githubgilhad/MegaHomeFORTH/docs/MHF-002/ATmega-Stacks.png

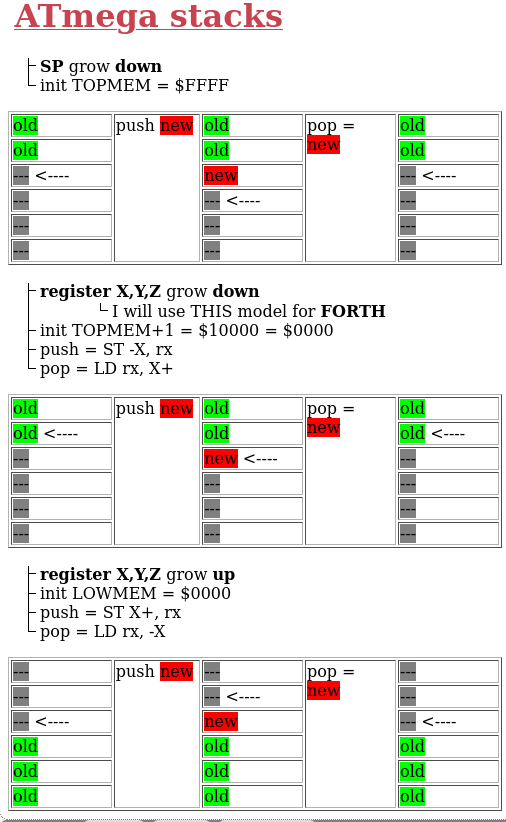
docs/MHF-002/ATmega-Stacks.png
