githubgilhad/MegaHomeFORTH/docs/MHF-002/config_gates.png

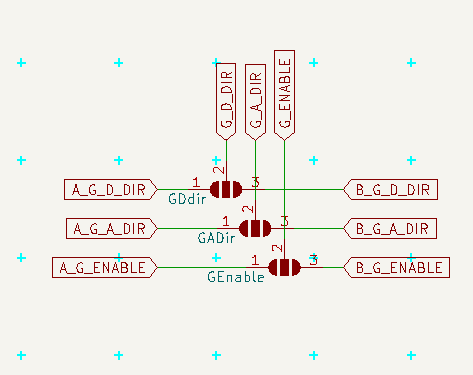
docs/MHF-002/config_gates.png
