githubgilhad/MegaHomeFORTH/docs/MHF-002/config_GLUE_top.png

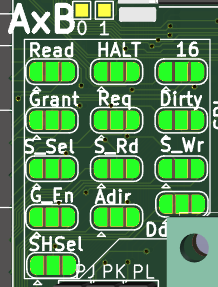
docs/MHF-002/config_GLUE_top.png
