githubgilhad/MegaHomeFORTH/docs/MHF-002/config_HALT_bottom.png

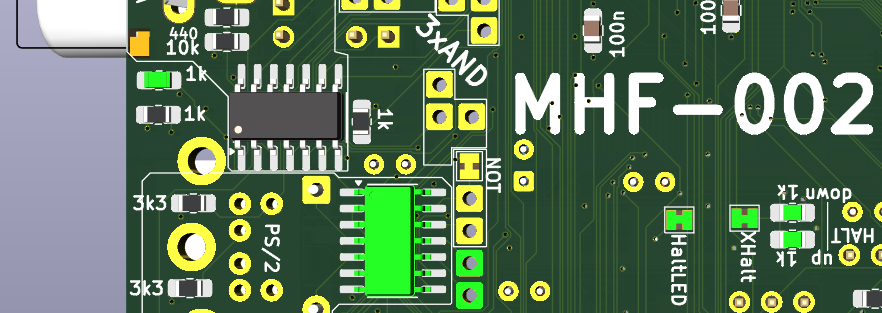
docs/MHF-002/config_HALT_bottom.png
