githubgilhad/MegaHomeFORTH/docs/MHF-002/config_SBC.png

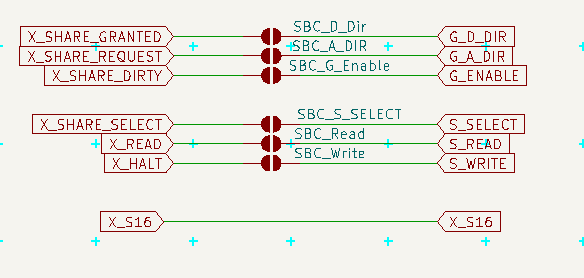
docs/MHF-002/config_SBC.png
