githubgilhad/MegaHomeFORTH/docs/MHF-002/config_shared.png

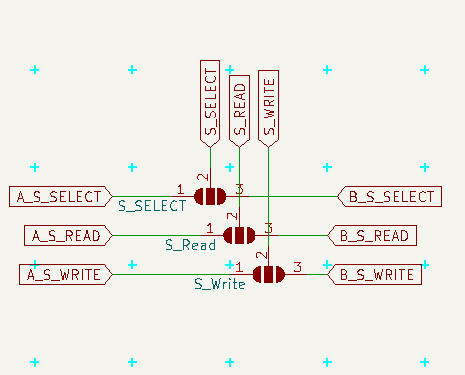
docs/MHF-002/config_shared.png
