githubgilhad/MegaHomeFORTH/docs/MHF-002/Expanduino_I_galerie_DSC_7885.s.jpg

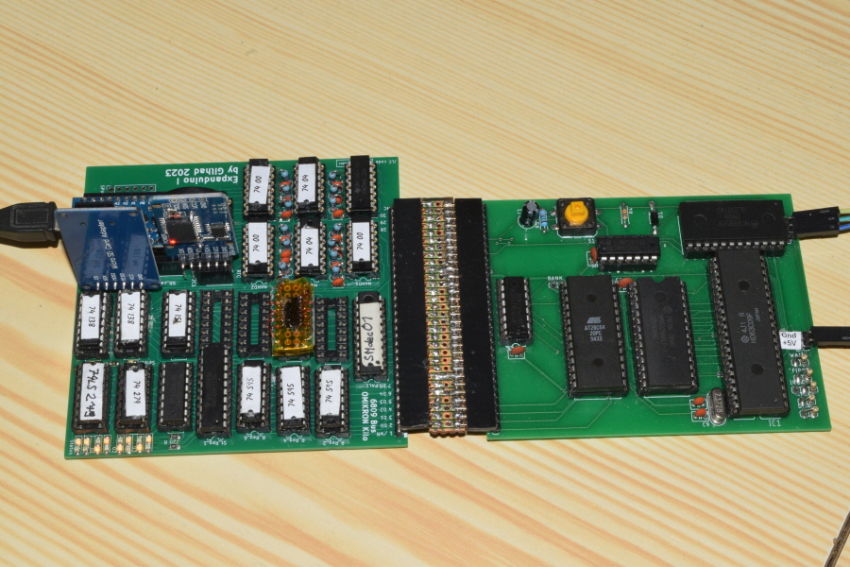
docs/MHF-002/Expanduino_I_galerie_DSC_7885.s.jpg
