githubgilhad/MegaHomeFORTH/docs/MHF-002/External_RAM_schema.png

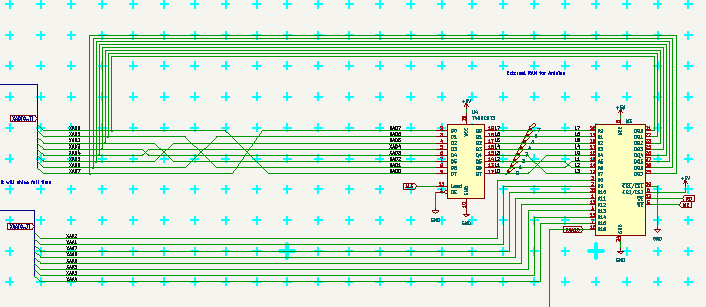
docs/MHF-002/External_RAM_schema.png
