githubgilhad/MegaHomeFORTH/docs/MHF-002/External_RAM_top.png

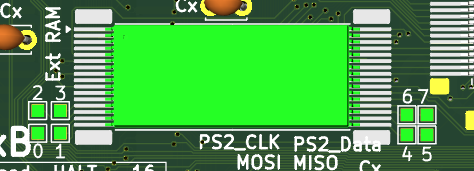
docs/MHF-002/External_RAM_top.png
