githubgilhad/MegaHomeFORTH/docs/MHF-002/FreeHand.png

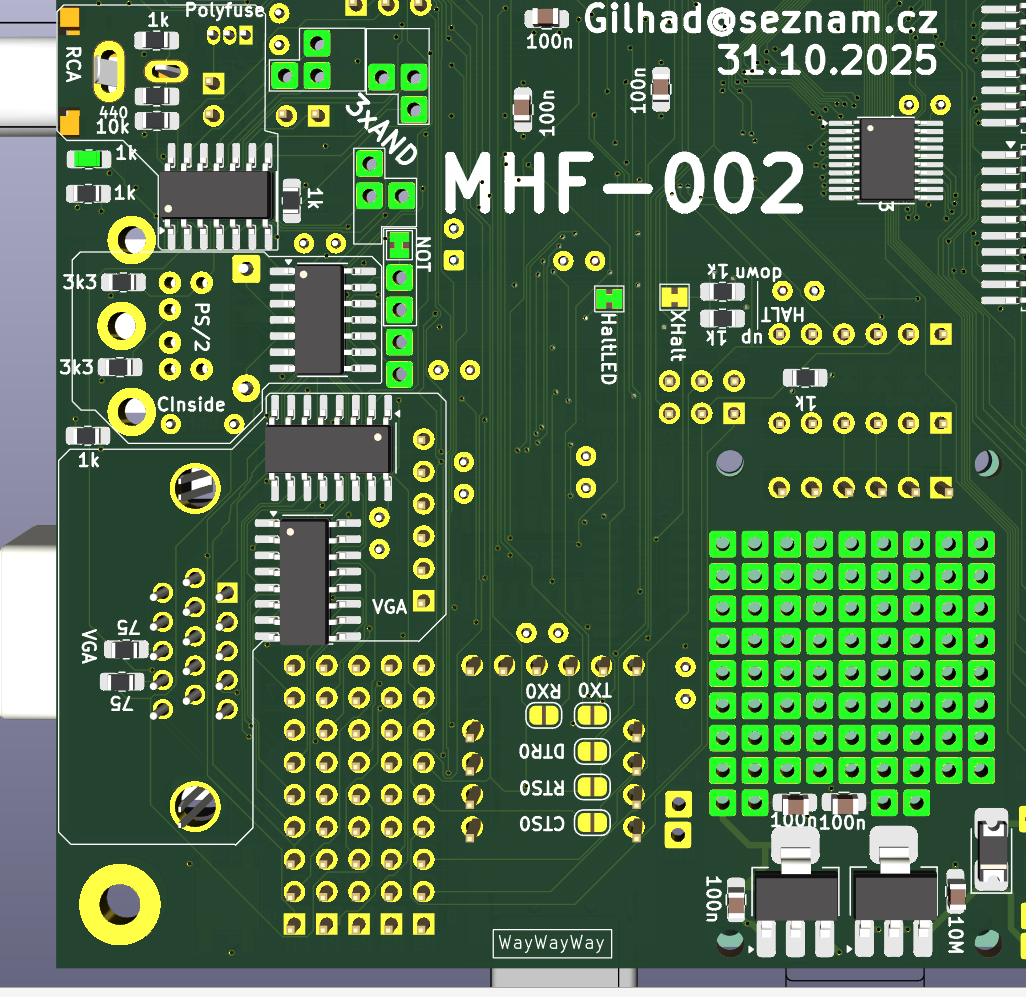
docs/MHF-002/FreeHand.png
