githubgilhad/MegaHomeFORTH/docs/MHF-002/PS2_botttom.png

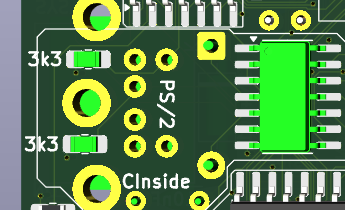
docs/MHF-002/PS2_botttom.png
