githubgilhad/MegaHomeFORTH/docs/MHF-002/PS2_direct_top.png

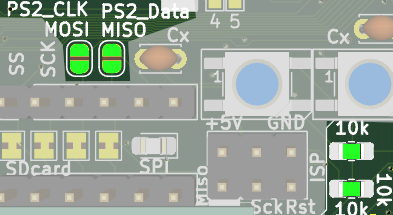
docs/MHF-002/PS2_direct_top.png
