githubgilhad/MegaHomeFORTH/docs/MHF-002/PS2_schema1.png

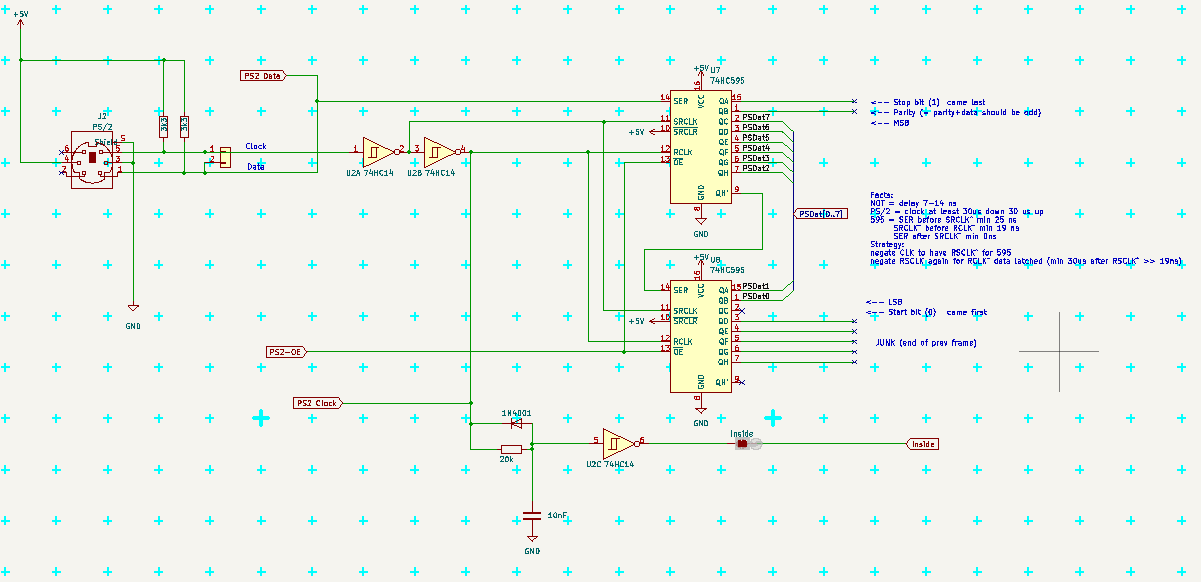
docs/MHF-002/PS2_schema1.png
