githubgilhad/MegaHomeFORTH/docs/MHF-002/PS2_schema2.png

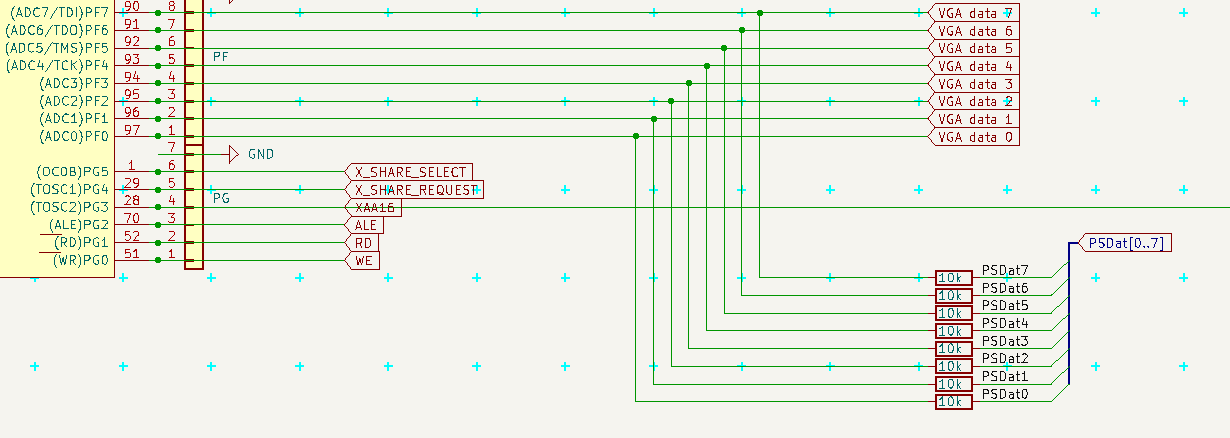
docs/MHF-002/PS2_schema2.png
