githubgilhad/MegaHomeFORTH/docs/MHF-002/PS2_top.png

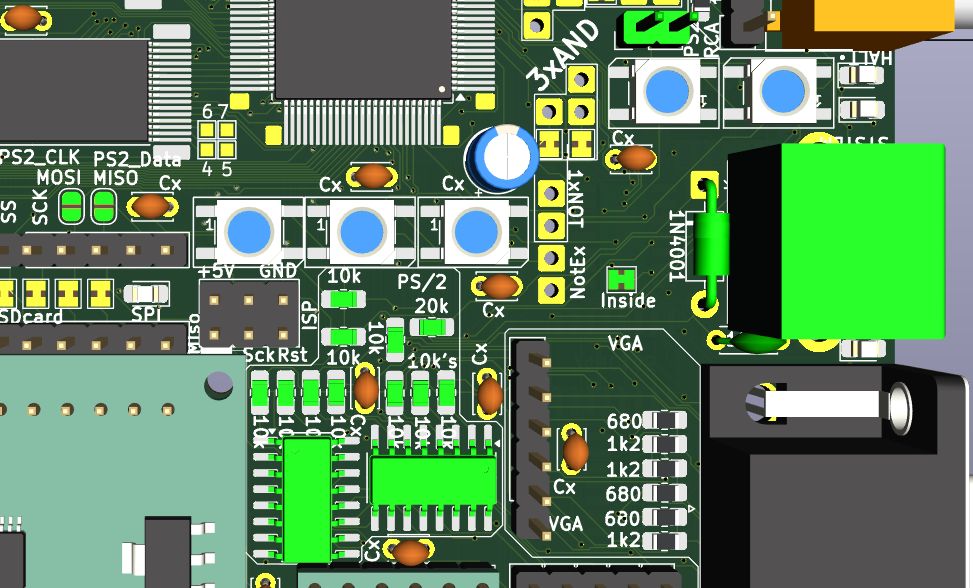
docs/MHF-002/PS2_top.png
