githubgilhad/MegaHomeFORTH/docs/MHF-002/RCA_bottom.png

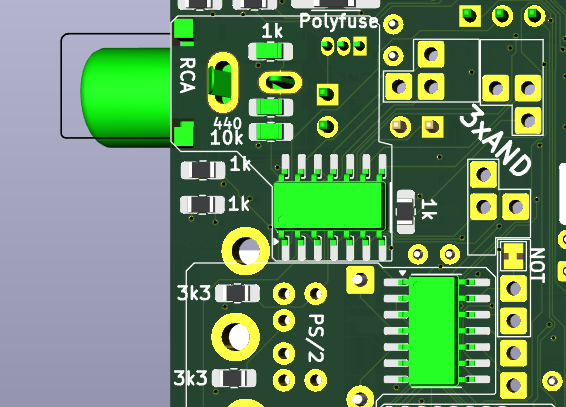
docs/MHF-002/RCA_bottom.png
