githubgilhad/MegaHomeFORTH/docs/MHF-002/RCA_schema.png

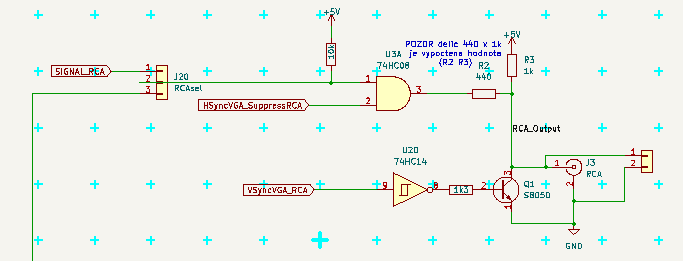
docs/MHF-002/RCA_schema.png
