githubgilhad/MegaHomeFORTH/docs/MHF-002/RCA_top.png

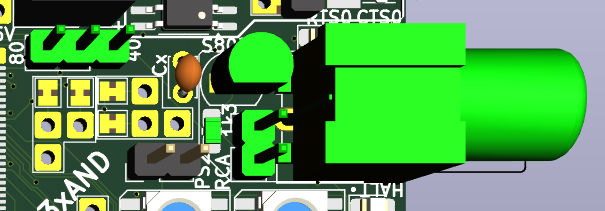
docs/MHF-002/RCA_top.png
