githubgilhad/MegaHomeFORTH/docs/MHF-002/Registers_C_Forth.png

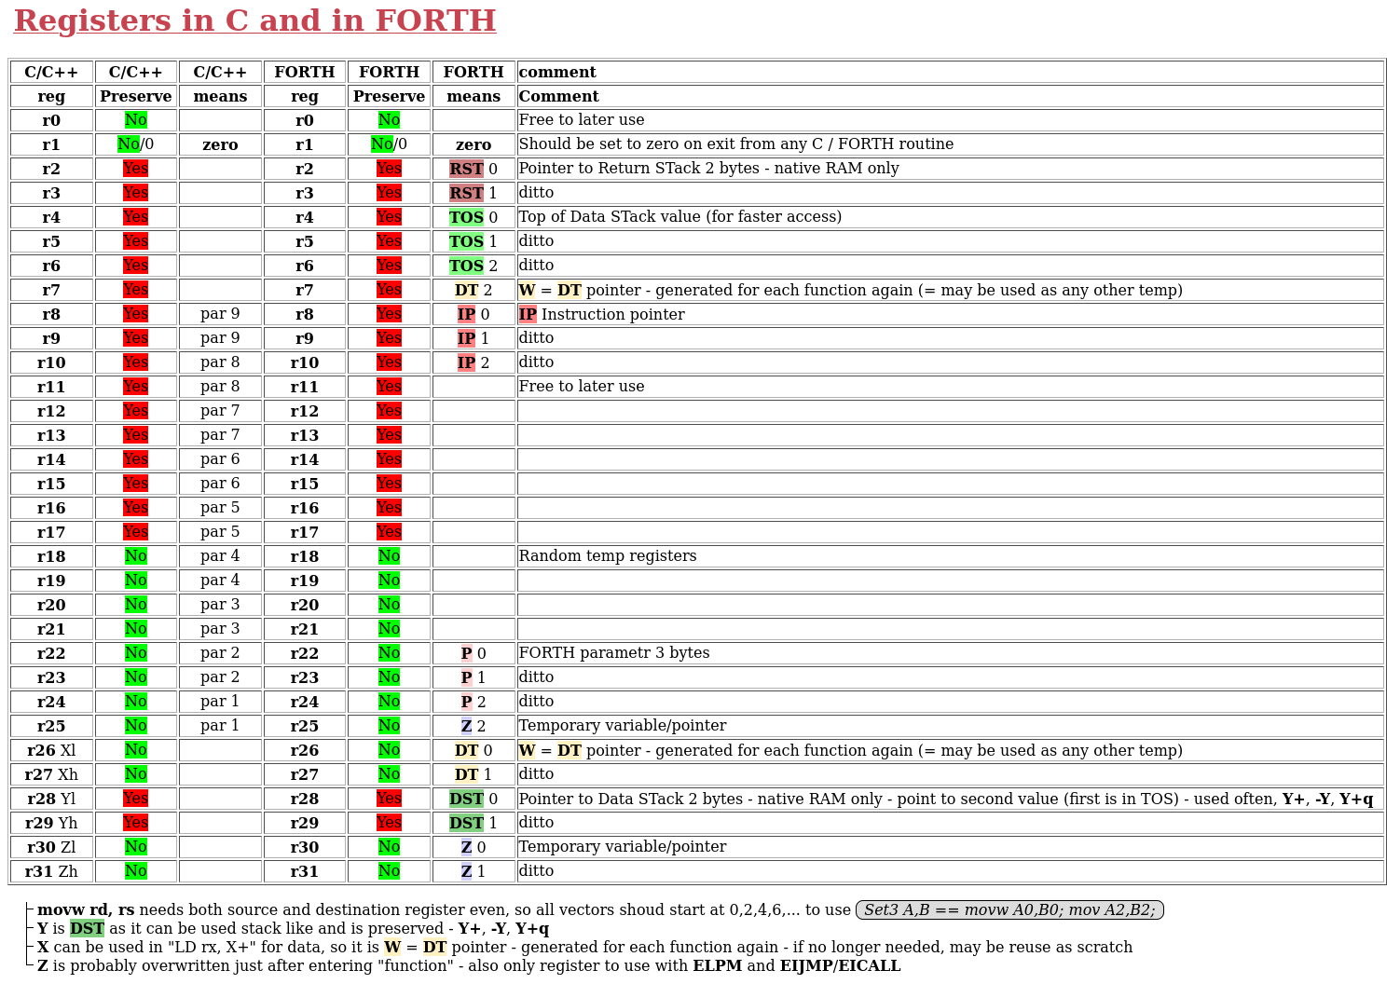
docs/MHF-002/Registers_C_Forth.png
