githubgilhad/MegaHomeFORTH/docs/MHF-002/RGB_LEDS_schema.png

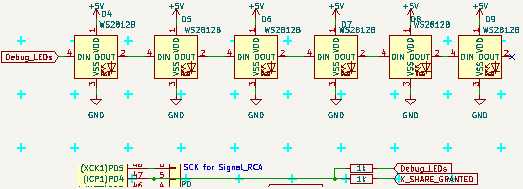
docs/MHF-002/RGB_LEDS_schema.png
