githubgilhad/MegaHomeFORTH/docs/MHF-002/RGB_LEDS_top.png

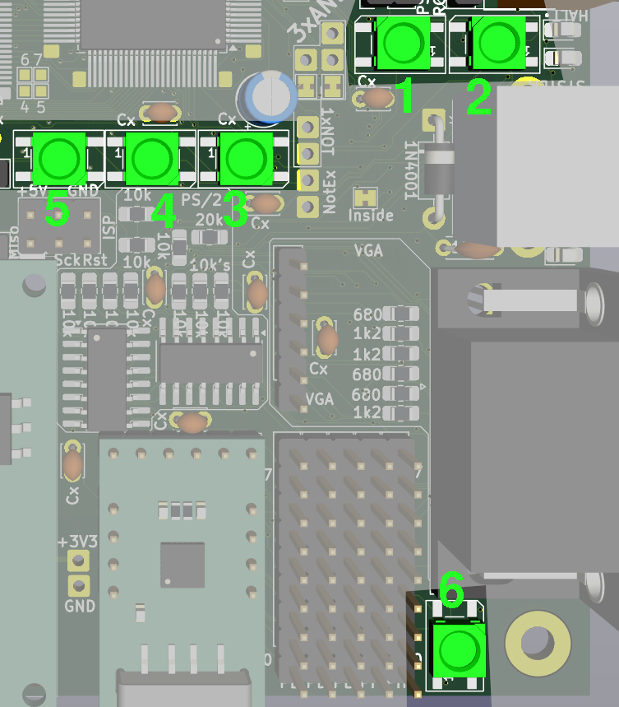
docs/MHF-002/RGB_LEDS_top.png
