githubgilhad/MegaHomeFORTH/docs/MHF-002/SD_schema.png

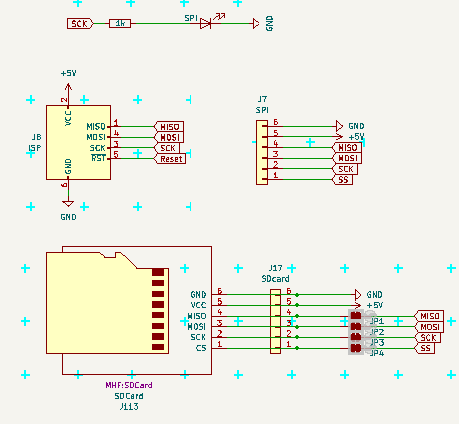
docs/MHF-002/SD_schema.png
