githubgilhad/MegaHomeFORTH/docs/MHF-002/SD_top.png

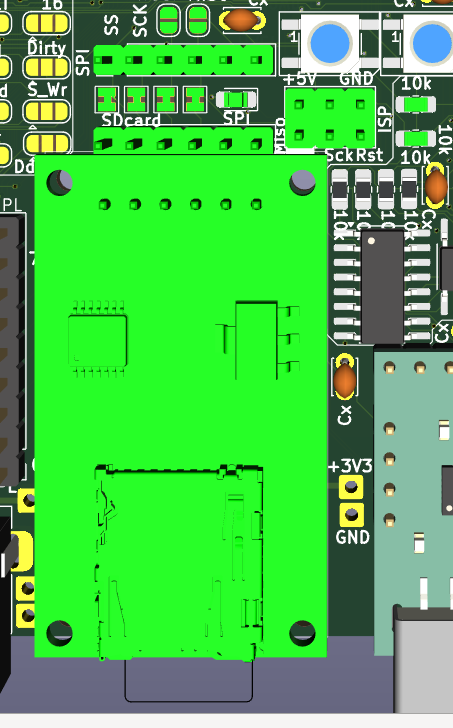
docs/MHF-002/SD_top.png
