githubgilhad/MegaHomeFORTH/docs/MHF-002/Shared_RAM_bottom.png

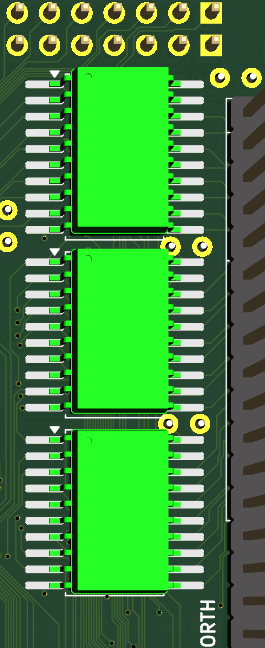
docs/MHF-002/Shared_RAM_bottom.png
