githubgilhad/MegaHomeFORTH/docs/MHF-002/Shared_RAM_schema.png

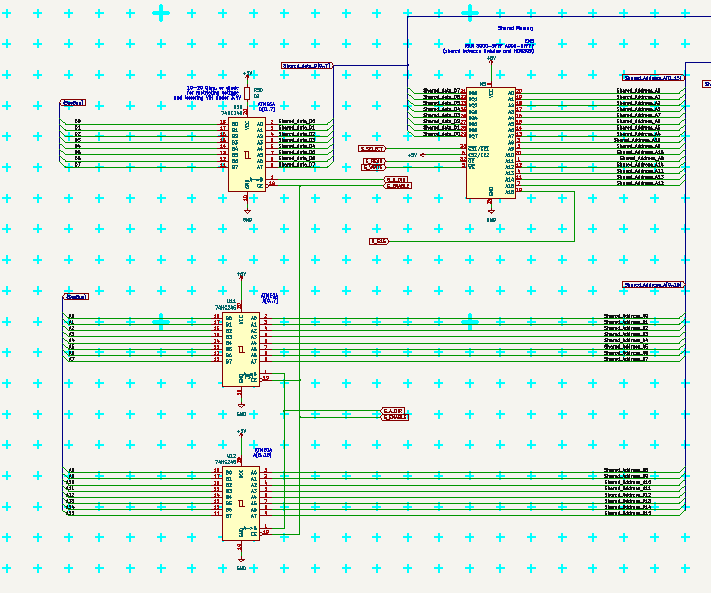
docs/MHF-002/Shared_RAM_schema.png
