githubgilhad/MegaHomeFORTH/docs/MHF-002/Shared_RAM_top.png

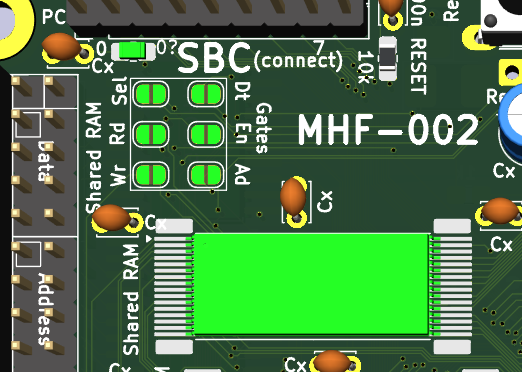
docs/MHF-002/Shared_RAM_top.png
