githubgilhad/MegaHomeFORTH/docs/MHF-002/SysBus.png

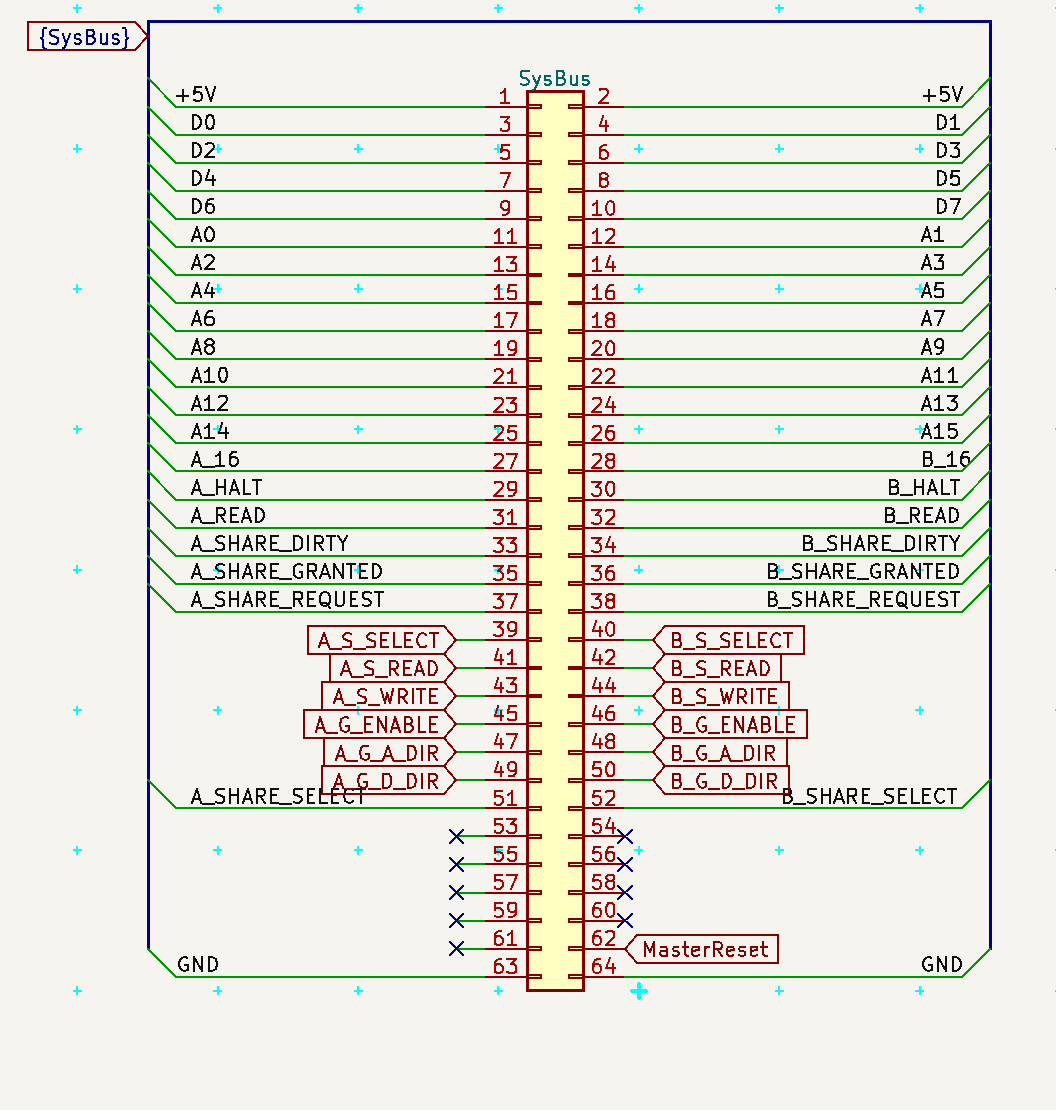
docs/MHF-002/SysBus.png
