githubgilhad/MegaHomeFORTH/docs/MHF-002/SystemBus-schema.png

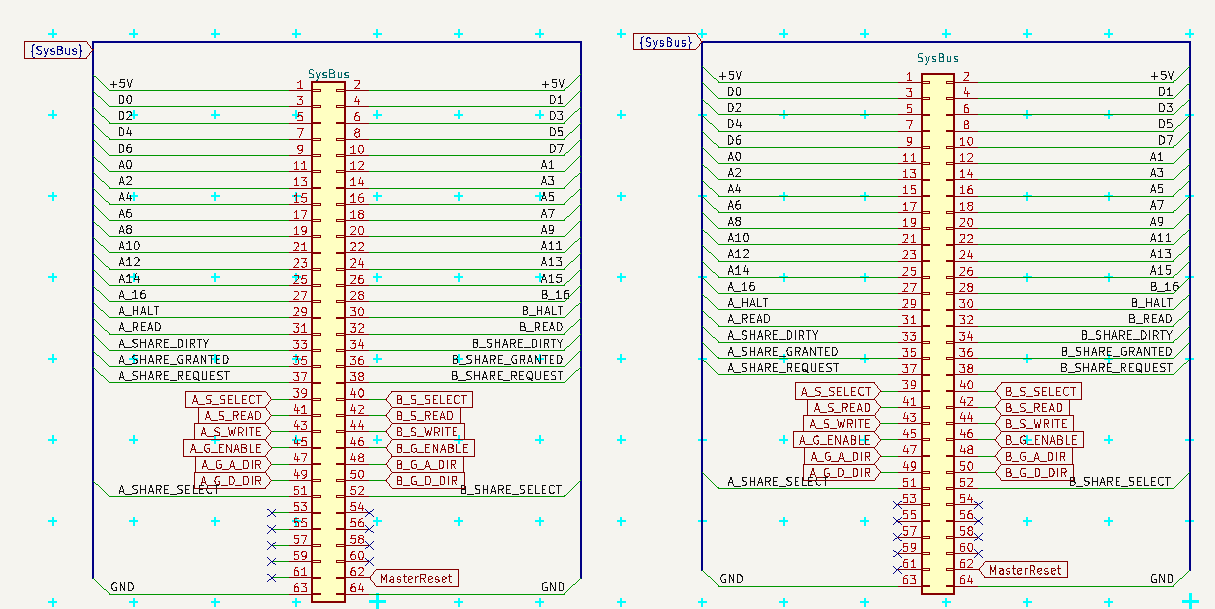
docs/MHF-002/SystemBus-schema.png
