githubgilhad/MegaHomeFORTH/docs/MHF-002/SystemBus-side.png

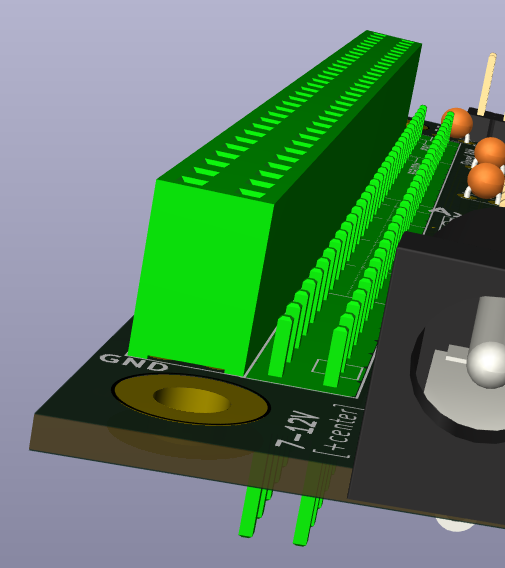
docs/MHF-002/SystemBus-side.png
