githubgilhad/MegaHomeFORTH/docs/MHF-002/USB-Serial_CH340G_top.png

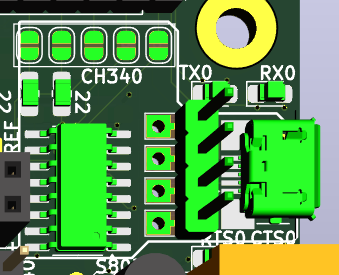
docs/MHF-002/USB-Serial_CH340G_top.png
