githubgilhad/MegaHomeFORTH/docs/MHF-002/USB-Serial_CP2102_top.png

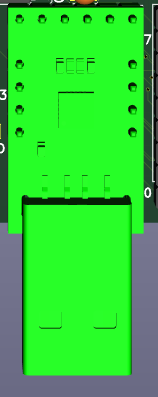
docs/MHF-002/USB-Serial_CP2102_top.png
