githubgilhad/MegaHomeFORTH/docs/MHF-002/USB-Serial_pinhead.png

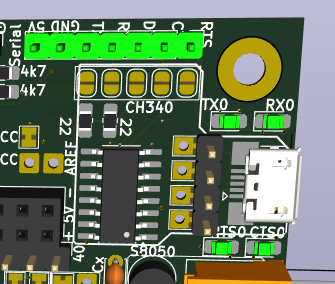
docs/MHF-002/USB-Serial_pinhead.png
