githubgilhad/MegaHomeFORTH/docs/MHF-002/USB-Serial_schema.png

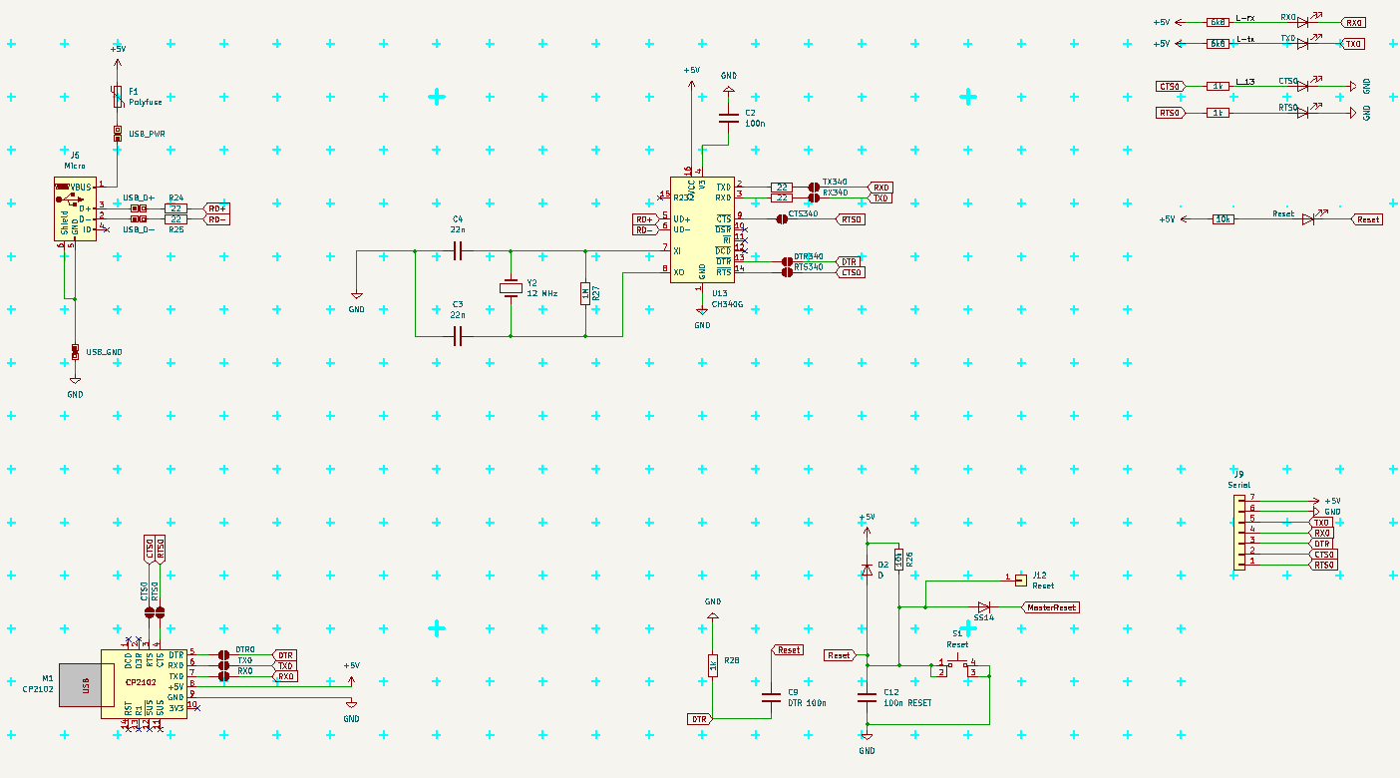
docs/MHF-002/USB-Serial_schema.png
