githubgilhad/MegaHomeFORTH/docs/retro-002.png

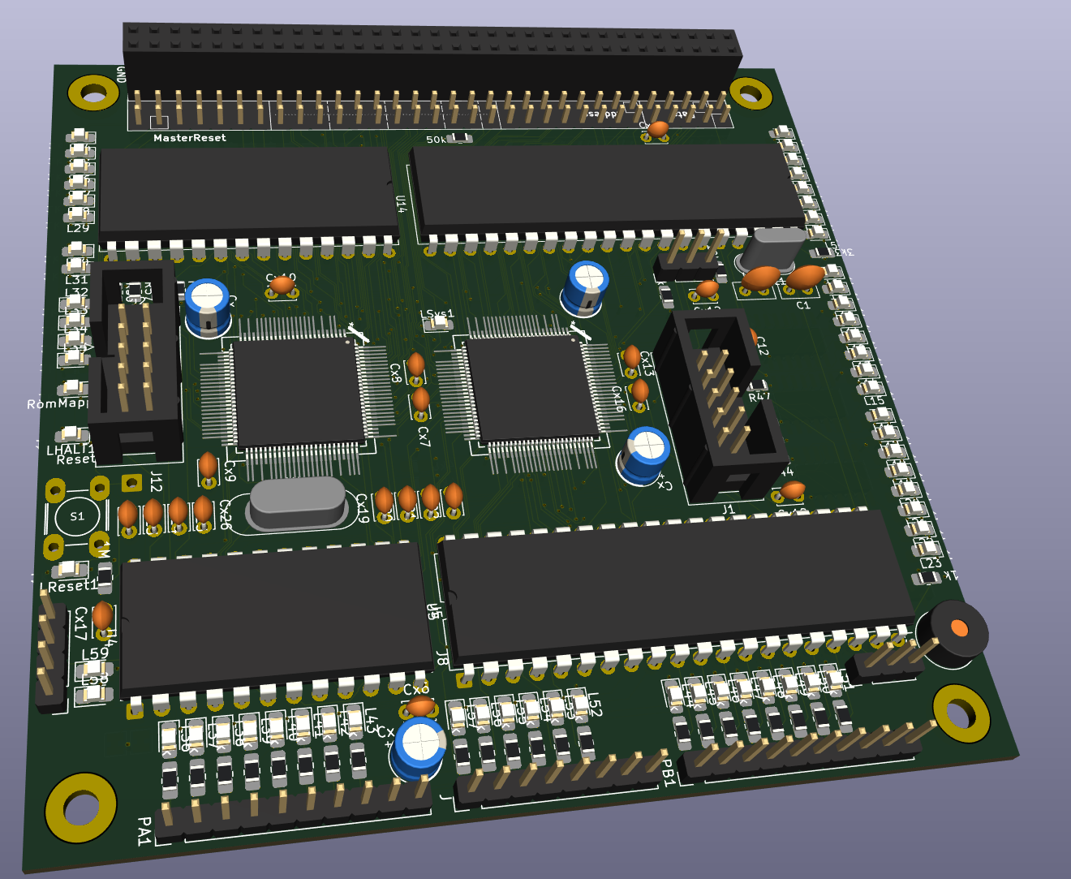
docs/retro-002.png
