githubgilhad/MegaHomeFORTH/HW/KiCad/ATmega2560-MegaPro-001/ATmega2560-MegaPro-001.schema.png

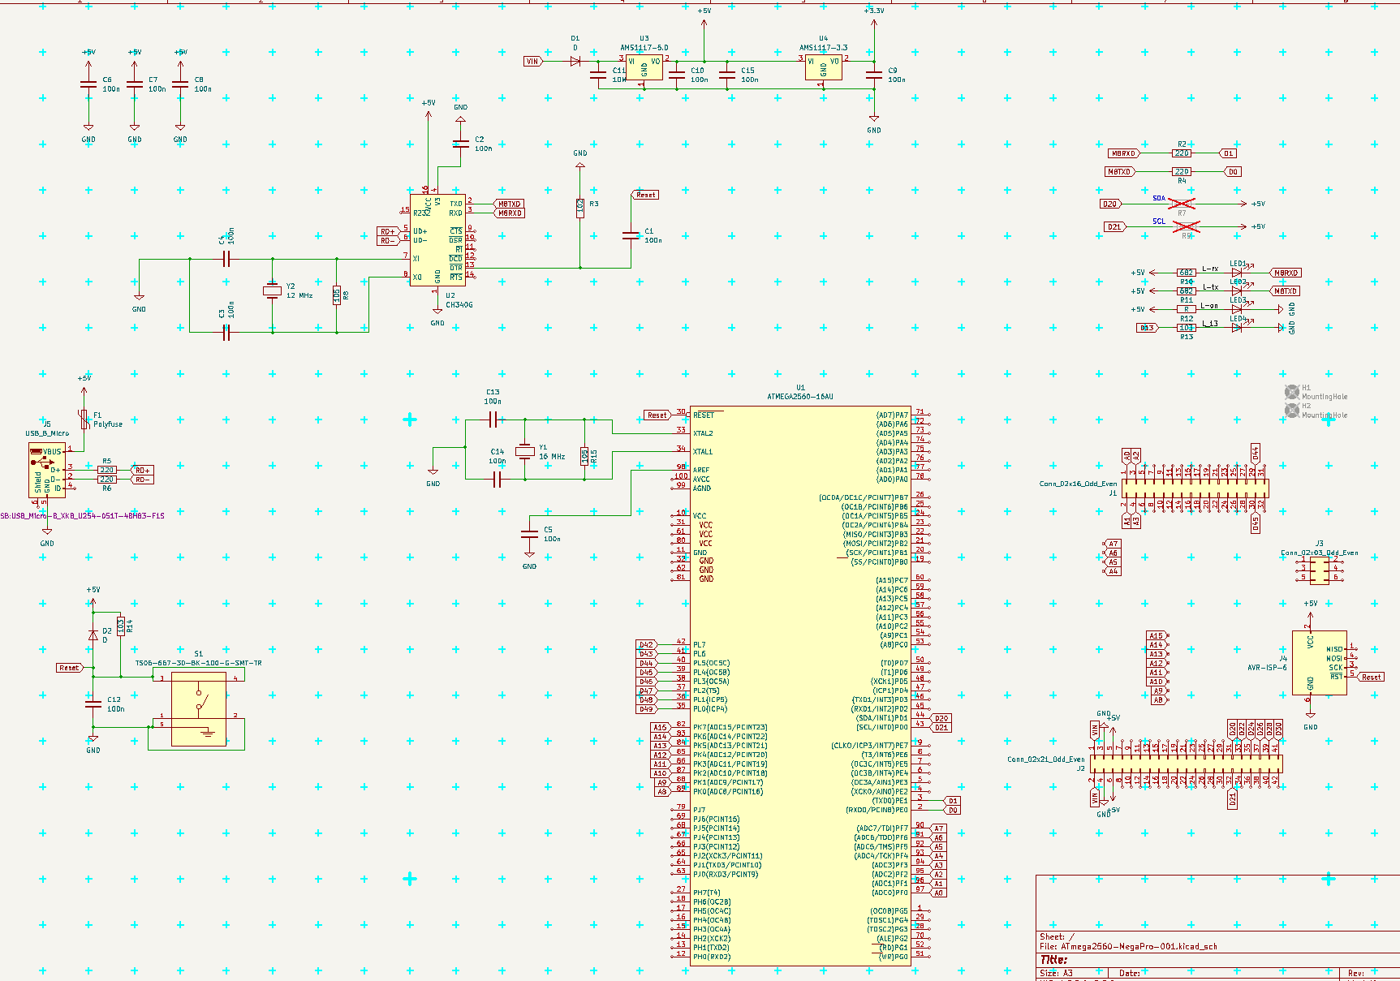
HW/KiCad/ATmega2560-MegaPro-001/ATmega2560-MegaPro-001.schema.png
