githubgilhad/MegaHomeFORTH/HW/KiCad/MHF-002/MHF-002.c.s.jpg

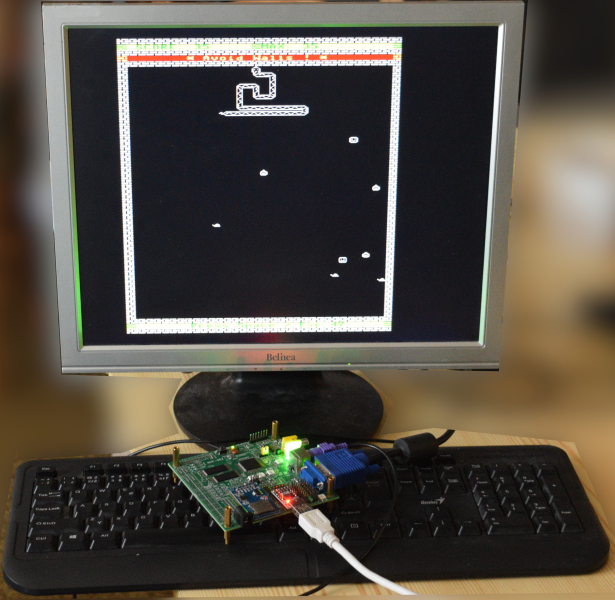
HW/KiCad/MHF-002/MHF-002.c.s.jpg
