githubgilhad/MegaHomeFORTH/HW/KiCad/Schema-8bitComp/Schema-8bitComp-BW.png

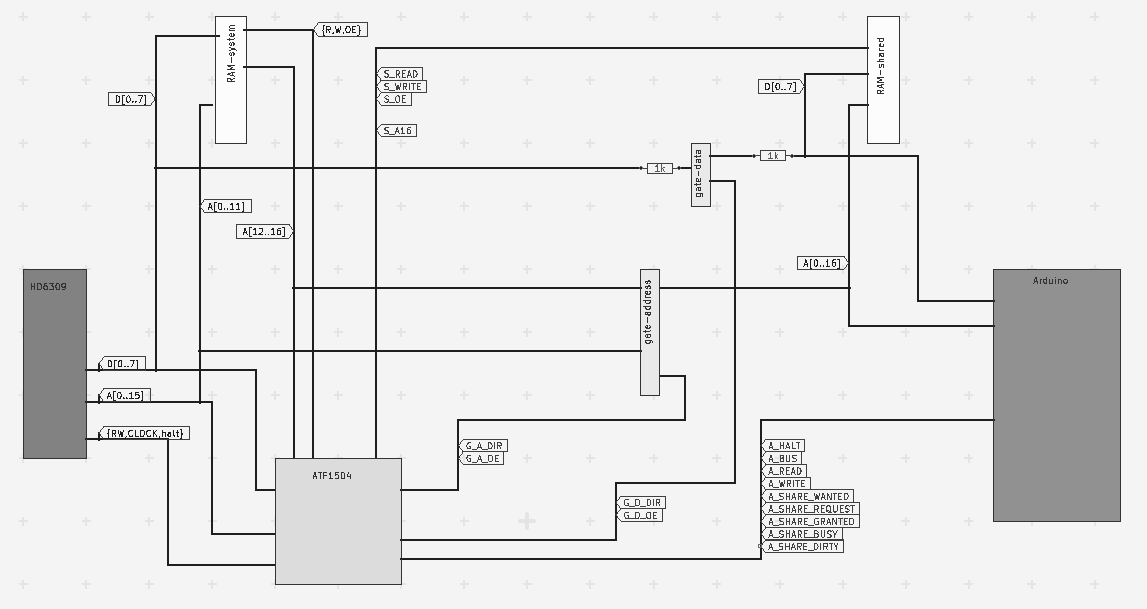
HW/KiCad/Schema-8bitComp/Schema-8bitComp-BW.png
