githubgilhad/MegaHomeFORTH/HW/KiCad/Schema-8bitComp/Schema-8bitComp.png

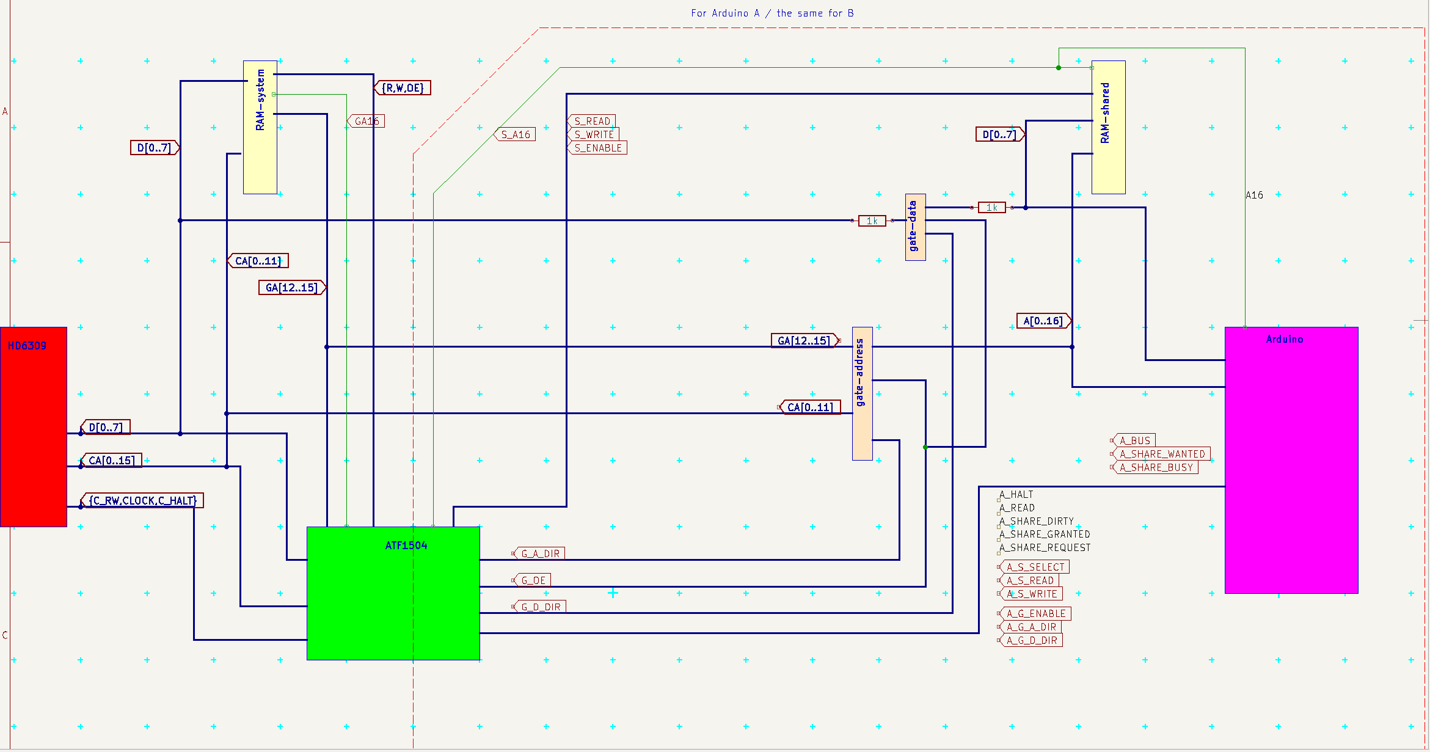
HW/KiCad/Schema-8bitComp/Schema-8bitComp.png
