githubgilhad/MegaHomeFORTH/photos/DSC_8351.s.jpg

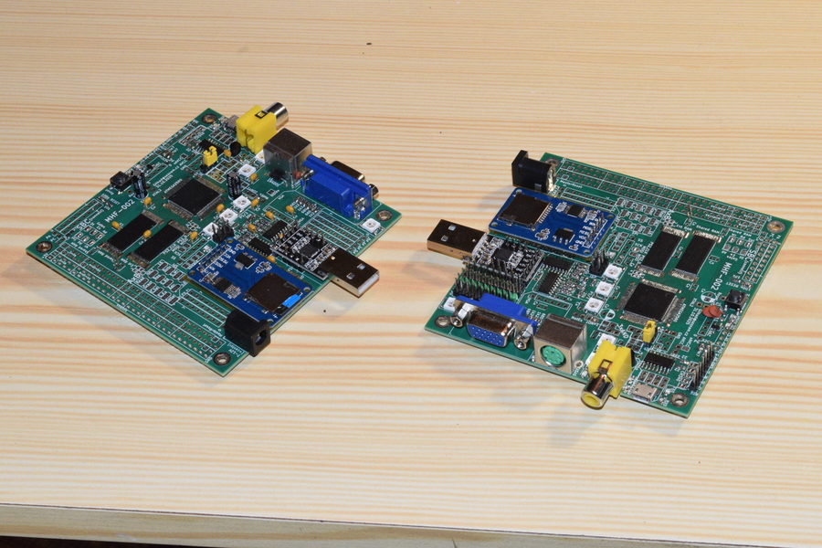
photos/DSC_8351.s.jpg
