githubgilhad/MegaHomeFORTH/photos/DSC_8371.s.jpg

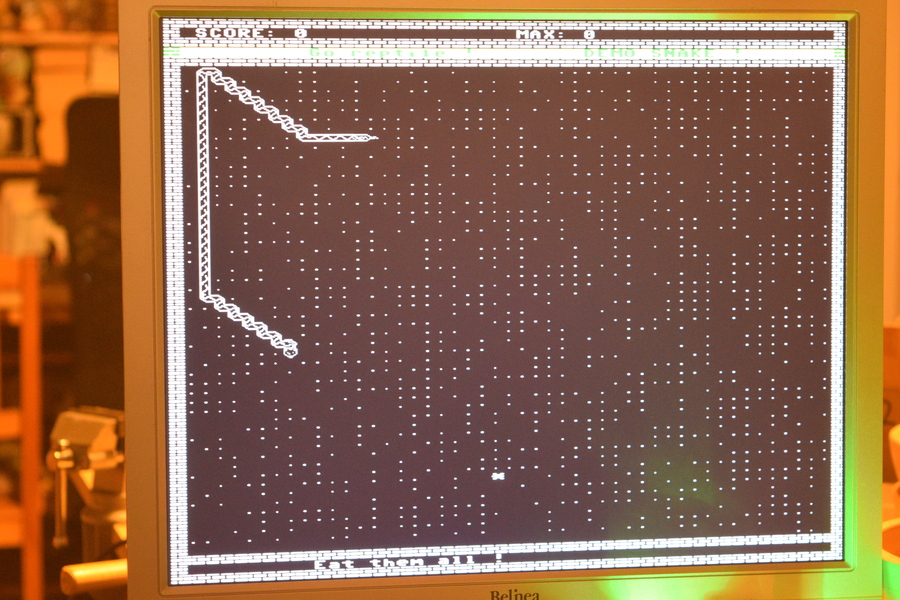
photos/DSC_8371.s.jpg
