githubgilhad/MegaHomeFORTH/photos/DSC_8372.s.jpg

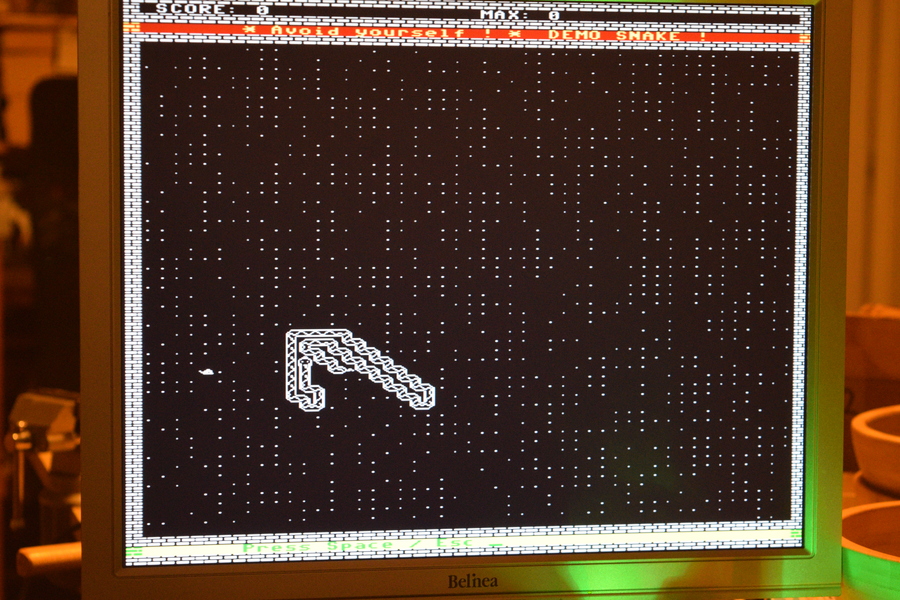
photos/DSC_8372.s.jpg
